Thecactusman0/Nebula-openwatch/Nebula - Master/Models/MCP73831T-2ATI_OT.step

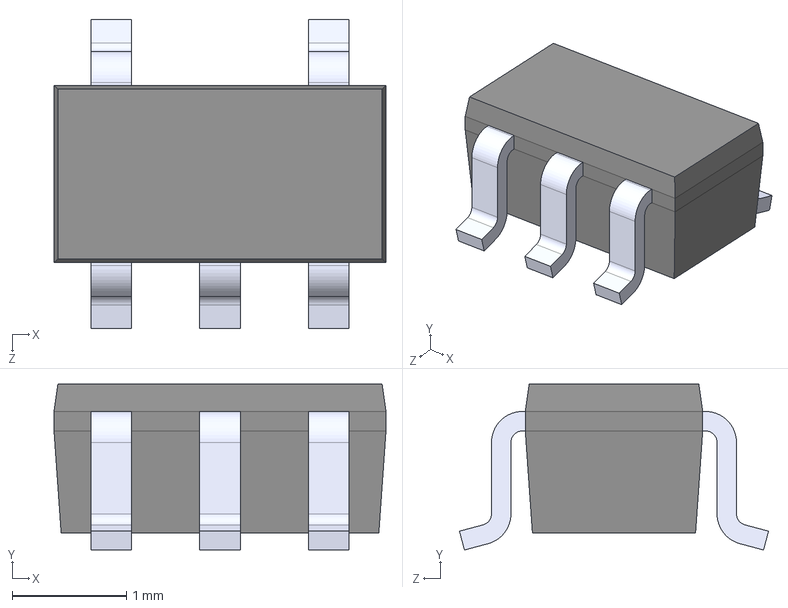
[picture p15: CAD file, 2022-09-09]
Nebula - Master/Models/MCP73831T-2ATI_OT.step
2.90 x 1.45 x 2.70 mm
