Thecactusman0/Nebula-openwatch/Nebula - Master/Code/Nebula os pc/bitmaps.cpp

#include "bitmaps.h"

const unsigned char stopwatchIcon[] PROGMEM = {
	0x00, 0x01, 0xff, 0x80, 0x00, 0x00, 0x01, 0xff, 0xc0, 0x00, 0x00, 0x01, 0xff, 0x80, 0x00, 0x00, 
	0x00, 0x1c, 0x00, 0x00, 0x00, 0x00, 0x1c, 0x00, 0x00, 0x00, 0x00, 0x1c, 0x00, 0x00, 0x00, 0x00, 
	0x3c, 0x00, 0x00, 0x00, 0x03, 0xff, 0x80, 0x00, 0x03, 0x0f, 0xff, 0xf0, 0x80, 0x07, 0xbf, 0xff, 
	0xf9, 0xc0, 0x07, 0xfe, 0x00, 0x7f, 0xe0, 0x03, 0xf8, 0x00, 0x1f, 0xc0, 0x01, 0xe0, 0x00, 0x0f, 
	0x80, 0x03, 0xc0, 0x00, 0x07, 0x80, 0x03, 0x80, 0x00, 0x03, 0xc0, 0x07, 0x80, 0x00, 0x01, 0xe0, 
	0x0f, 0x00, 0x00, 0x00, 0xe0, 0x0e, 0x00, 0x30, 0x00, 0xe0, 0x0e, 0x00, 0x30, 0x00, 0x70, 0x0e, 
	0x00, 0x30, 0x00, 0x70, 0x1c, 0x00, 0x30, 0x00, 0x78, 0x1c, 0x00, 0x30, 0x00, 0x78, 0x1c, 0x00, 
	0x30, 0x00, 0x78, 0x1c, 0x00, 0x38, 0x00, 0x78, 0x1c, 0x00, 0x3f, 0x80, 0x78, 0x1c, 0x00, 0x3f, 
	0x80, 0x78, 0x1e, 0x00, 0x00, 0x00, 0x70, 0x0e, 0x00, 0x00, 0x00, 0x70, 0x0e, 0x00, 0x00, 0x00, 
	0xf0, 0x0f, 0x00, 0x00, 0x00, 0xe0, 0x07, 0x00, 0x00, 0x01, 0xe0, 0x07, 0x80, 0x00, 0x01, 0xc0, 
	0x03, 0xc0, 0x00, 0x03, 0xc0, 0x01, 0xe0, 0x00, 0x07, 0x80, 0x01, 0xf0, 0x00, 0x0f, 0x00, 0x00, 
	0xfc, 0x00, 0x3e, 0x00, 0x00, 0x3f, 0x81, 0xfc, 0x00, 0x00, 0x1f, 0xff, 0xf0, 0x00, 0x00, 0x07, 
	0xff, 0xe0, 0x00, 0x00, 0x00, 0xff, 0x00, 0x00
};

const unsigned char accelerometerIcon [] PROGMEM = {
	0x00, 0x00, 0x00, 0x00, 0x00, 0x00, 0x00, 0x08, 0x00, 0x00, 0x00, 0x00, 0x3c, 0x00, 0x00, 0x00, 
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
	0x00, 0x01, 0xff, 0x80, 0x00, 0x00, 0x00, 0xff, 0x00, 0x00, 0x00, 0x00, 0xff, 0x00, 0x00, 0x00, 
	0x00, 0x7e, 0x00, 0x00, 0x00, 0x00, 0x00, 0x00, 0x00, 0x00, 0x00, 0x00, 0x00, 0x00, 0x00, 0x00, 
	0x00, 0x00, 0x00, 0x00, 0x00, 0x00, 0x00, 0x00
};
