Thecactusman0/Nebula-openwatch/Nebula - Master/Code/Nebula os pc/bitmaps.h

#ifndef BITMAPS_H
#define BITMAPS_H
#include <Arduino.h>
//#include <pgmspace.h>

extern const unsigned char stopwatchIcon[224] PROGMEM;
extern const unsigned char accelerometerIcon [224] PROGMEM;
extern const unsigned char gyroscopeIcon [224] PROGMEM;
extern const unsigned char bluetoothIcon [496] PROGMEM;
extern const unsigned char microphoneIcon [224] PROGMEM;
extern const unsigned char speakerIcon [368] PROGMEM;
extern const unsigned char wrenchIcon [144] PROGMEM;
extern const unsigned char wifiIcon [224] PROGMEM;
#endif
