Thecactusman0/Nebula-openwatch/Nebula - Master/Code/Nebula os pc/wifi_update.h

#ifndef WIFI_UPDATE_H
#define WIFI_UPDATE_H
#include "Arduino.h"
//#include <WiFi.h>
//#include <ESPmDNS.h>
//#include <WiFiUdp.h>
//#include <ArduinoOTA.h>

extern const char* ssid;
extern const char* password;
void arduinoOTA();
#endif
